Echoras/Cortex-Command/3D files/washer-middle.stl

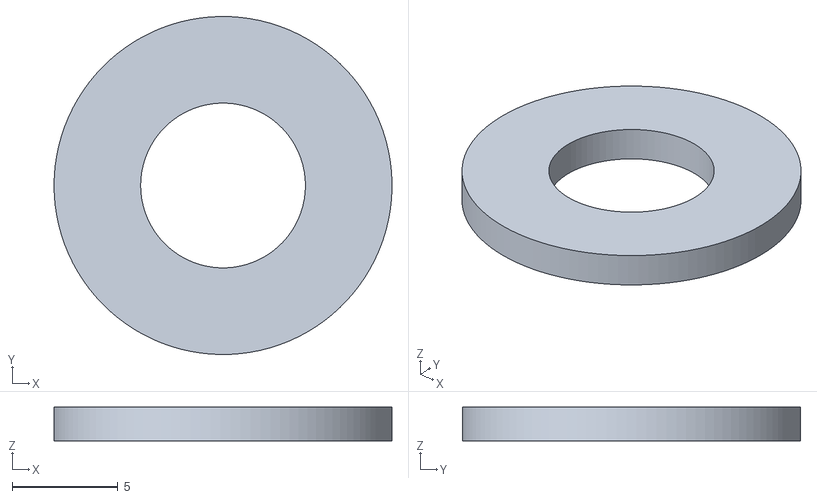
[picture p23: CAD file, 2025-12-18]
3D files/washer-middle.stl
16.0 x 16.0 x 1.60
