Echoras/Cortex-Command/3D files/washer-sleeve-a.stl

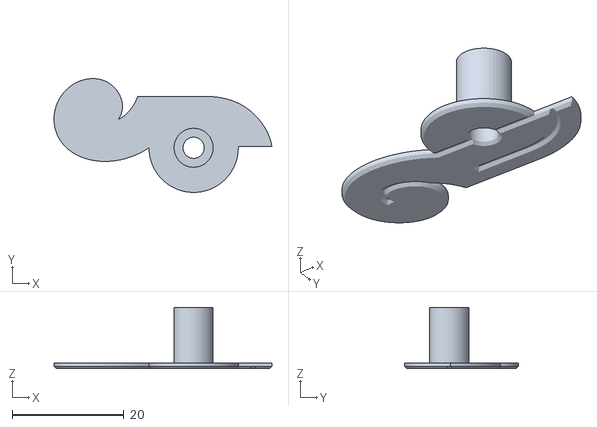
[picture p24: CAD file, 2025-12-18]
3D files/washer-sleeve-a.stl
39.0 x 20.4 x 11.0
